EduDemoS/demo.modular/model/Water-Module/Upper_Ring__Water_Module.stl

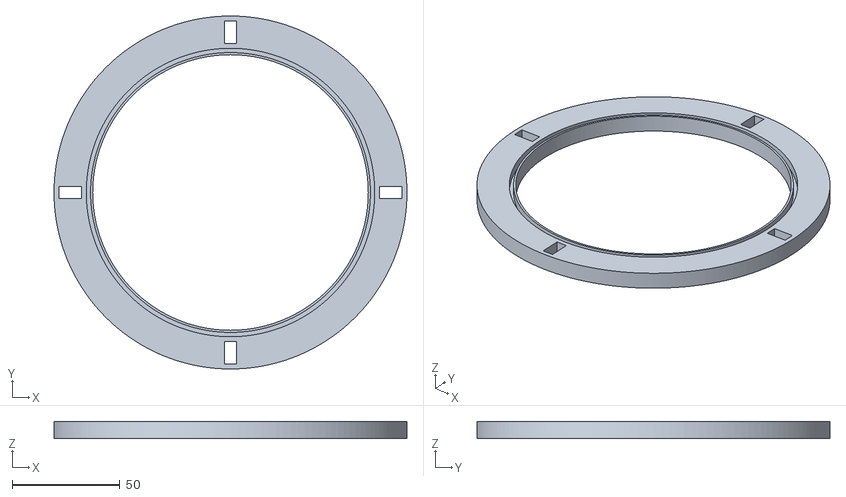
[picture p15: CAD file, 2025-07-11]
model/Water-Module/Upper_Ring__Water_Module.stl
164.0 x 164.0 x 8.00
