EduDemoS/demo.modular/model/Water-Module/x4_Cactus__Water_Module.stl

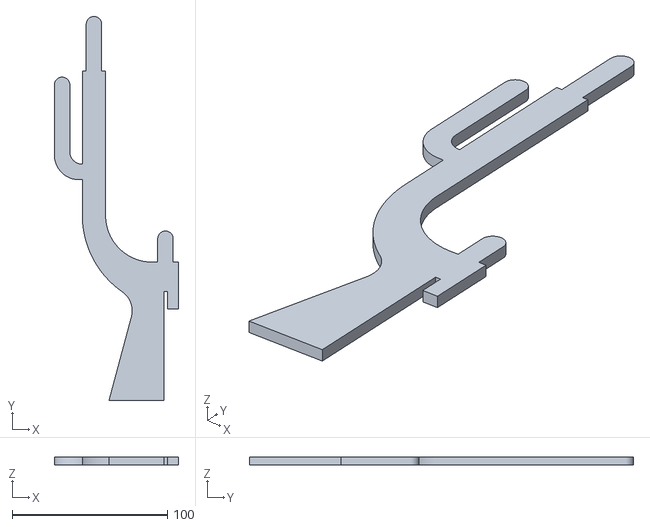
[picture p16: CAD file, 2025-07-11]
model/Water-Module/x4_Cactus__Water_Module.stl
80.0 x 247.0 x 5.00
